frankyhub/Bird_watching/pic/Bird watching3.png

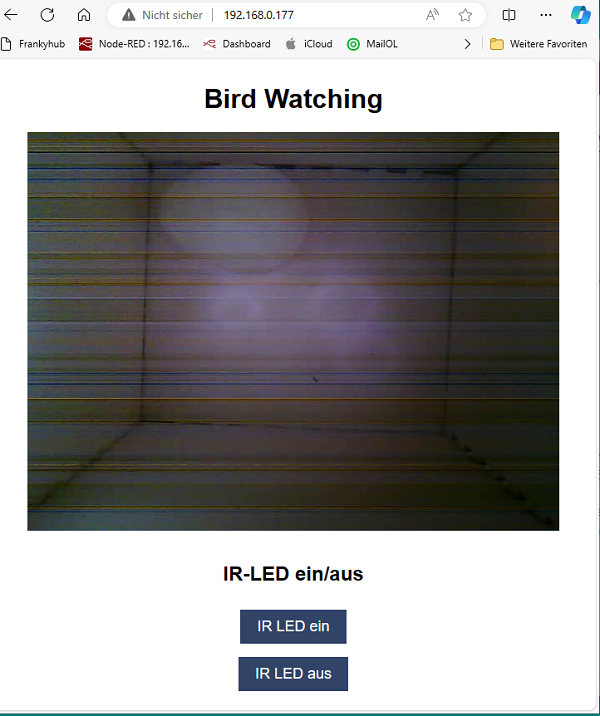
pic/Bird watching3.png
