frankyhub/Bird_watching/pic/ESP32-CAM-Lid2.png

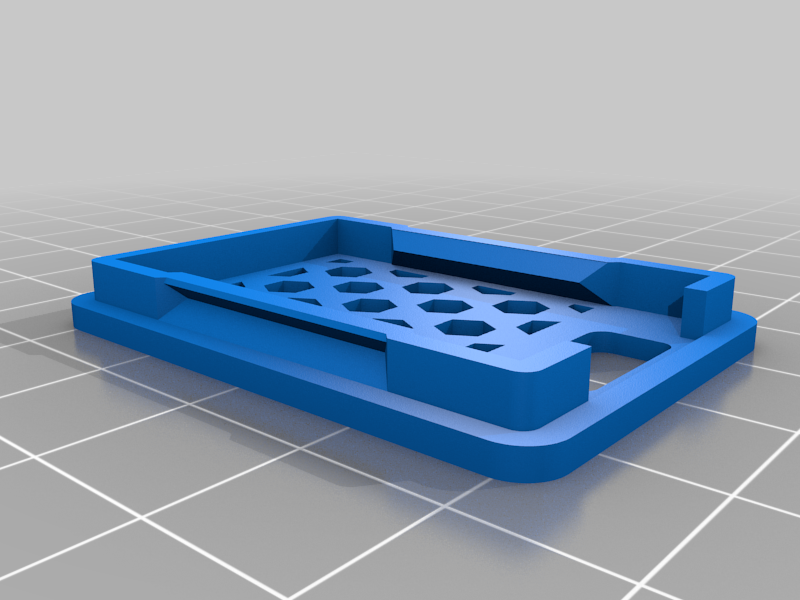
pic/ESP32-CAM-Lid2.png
