frankyhub/Bird_watching/pic/meisenkasten 1.jpg

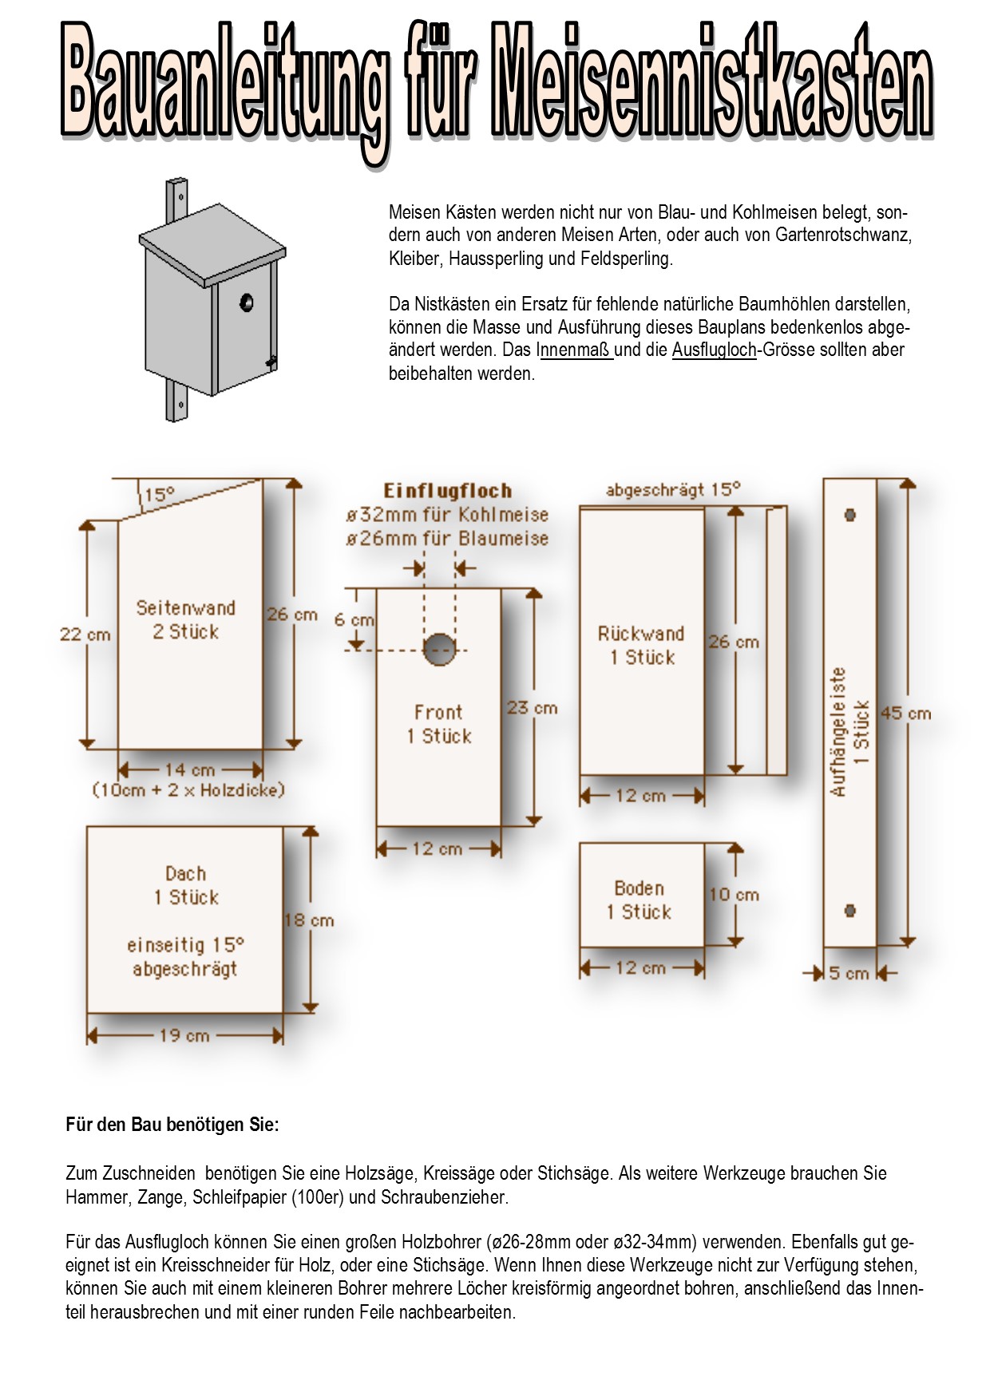
pic/meisenkasten 1.jpg
