frankyhub/Bird_watching/pic/meisenkasten 2.jpg

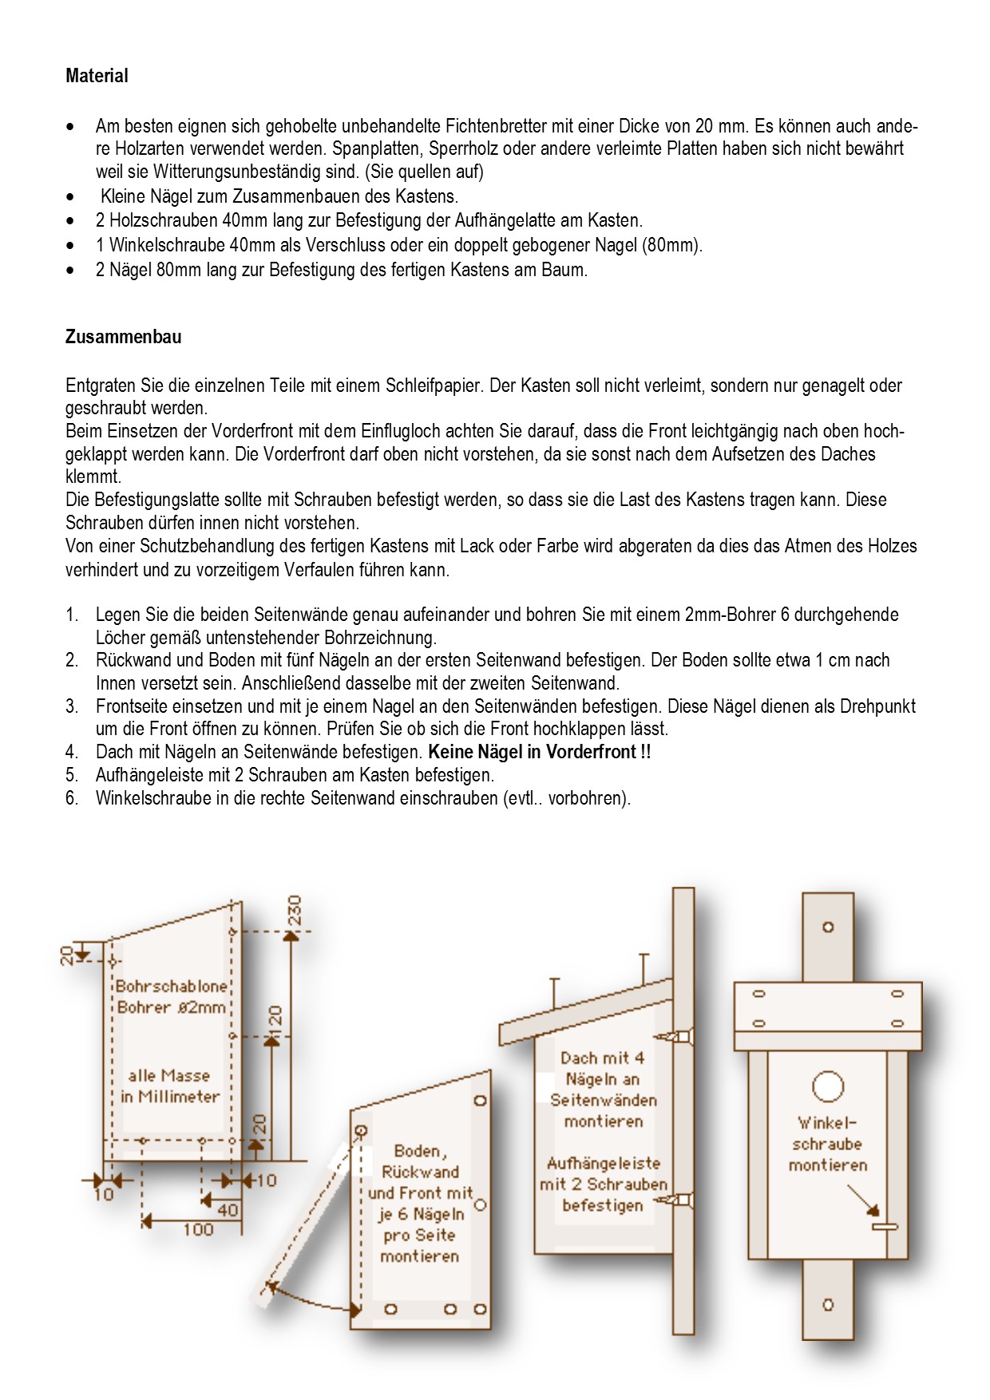
pic/meisenkasten 2.jpg
