frankyhub/Bird_watching/pic/Rear_box_ESP32_2.jpg

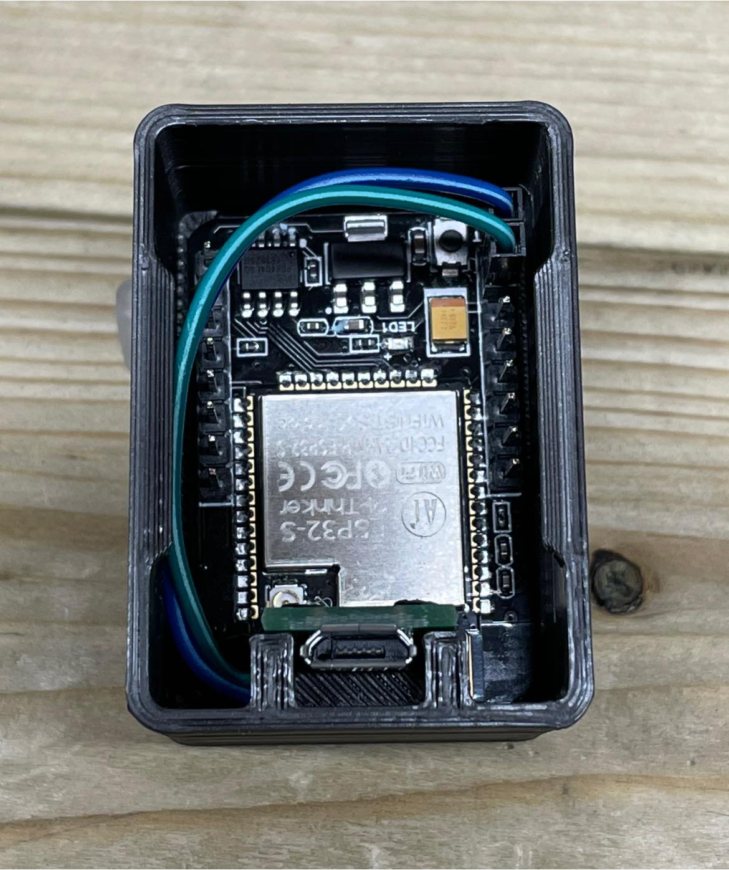
pic/Rear_box_ESP32_2.jpg
